PGRacing/PDM/SIM/CALCULATIONS/trace_width_proprties/external_12mm_1oz_10A_result.JPG

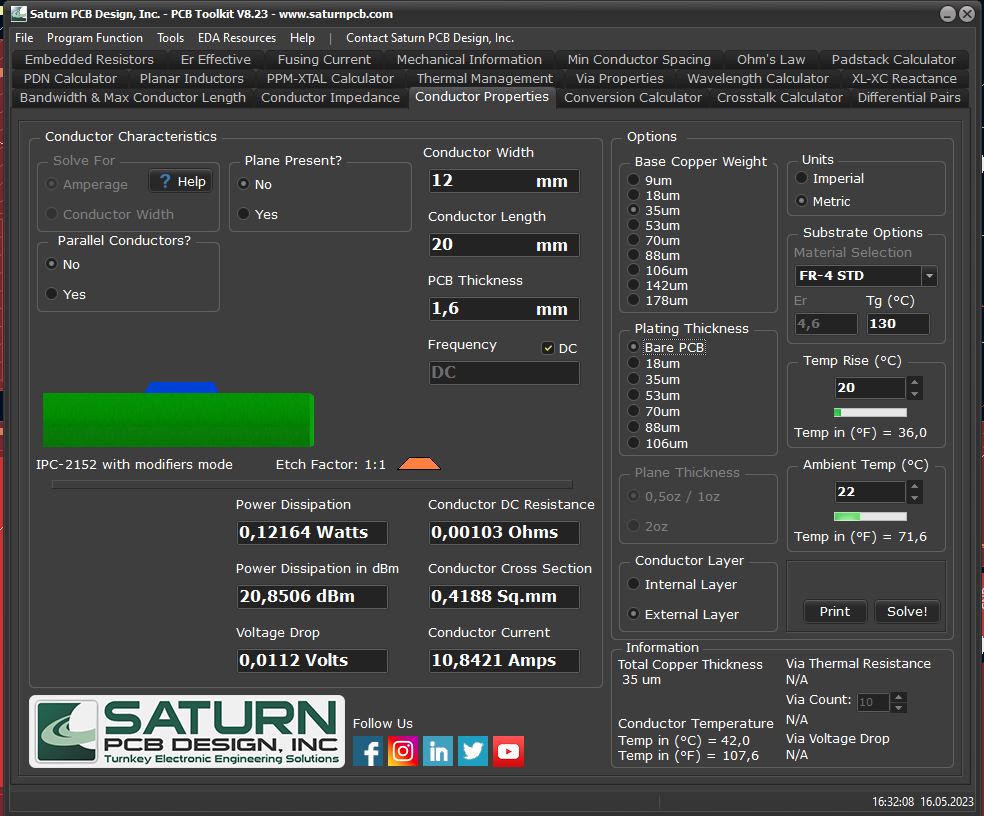
SIM/CALCULATIONS/trace_width_proprties/external_12mm_1oz_10A_result.JPG
