PGRacing/PDM/MODEL/CASE_2025/pdms_assy_2025.SLDASM

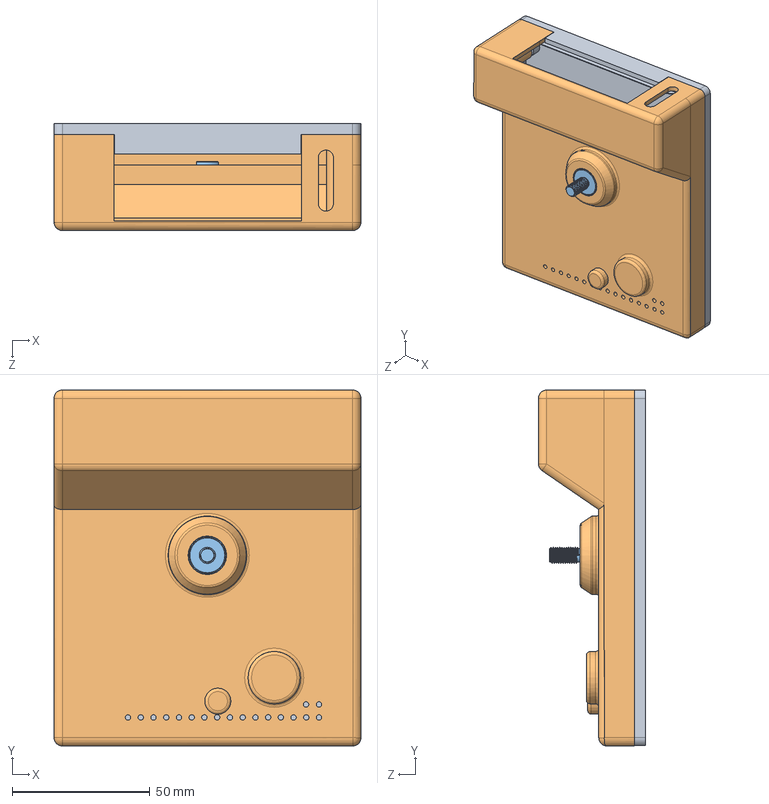
[picture p14: CAD file, 2026-06-07]
MODEL/CASE_2025/pdms_assy_2025.SLDASM
111.5 x 129.3 x 38.9 mm
pdms_thread_extender
pdms_upper_case
pdms_lower_case
