PGRacing/PDM/PCB/PDMS/pdms_additional/SPBTLE-RF/SPBTLE-RF.step

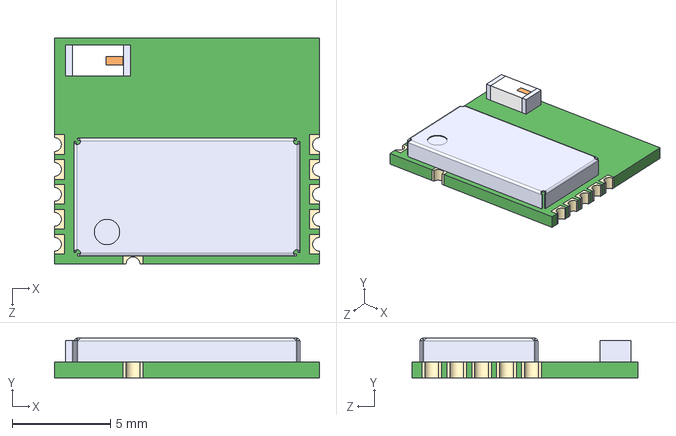
[picture p29: CAD file, 2023-05-31]
PCB/PDMS/pdms_additional/SPBTLE-RF/SPBTLE-RF.step
13.5 x 2.02 x 11.5 mm
