PGRacing/PDM/PCB/PDMS/pdms_additional/WS2812B-2020/WS2812B-2020.stp

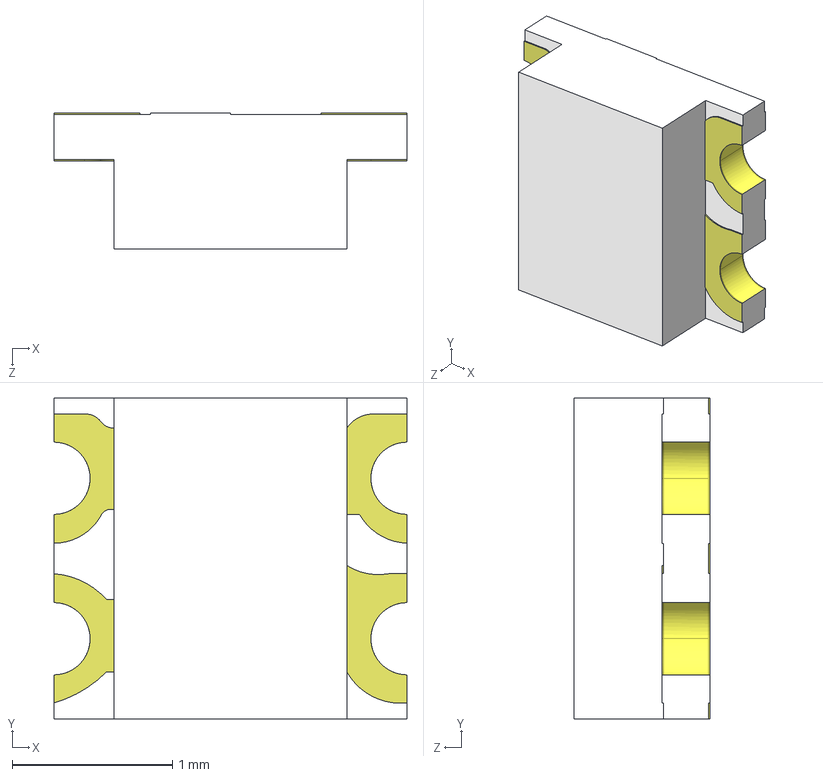
[picture p30: CAD file, 2023-05-21]
PCB/PDMS/pdms_additional/WS2812B-2020/WS2812B-2020.stp
2.20 x 2.00 x 0.85 mm
