PGRacing/PDM/MODEL/CASE_2025/pdms_thread_extender.SLDPRT

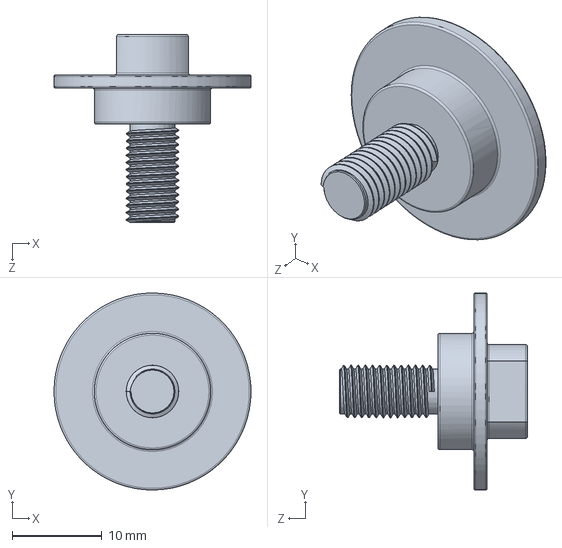
[picture p31: CAD file, 2026-06-07]
MODEL/CASE_2025/pdms_thread_extender.SLDPRT
22.0 x 22.0 x 21.0 mm
