PGRacing/PDM/MODEL/CASE_2024/upper.SLDPRT

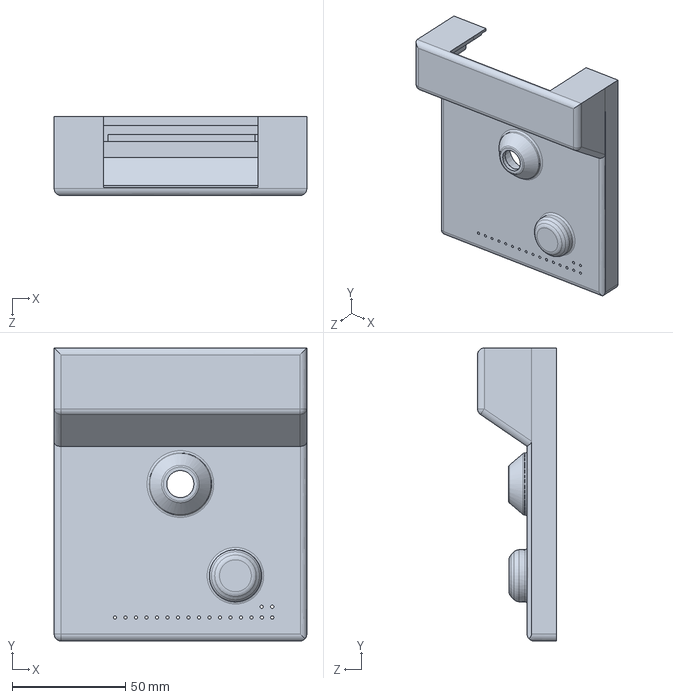
[picture p32: CAD file, 2026-06-07]
MODEL/CASE_2024/upper.SLDPRT
111.5 x 129.3 x 34.9 mm
