PGRacing/PDM/MODEL/CASE_2025/pdms_lower_case.SLDPRT

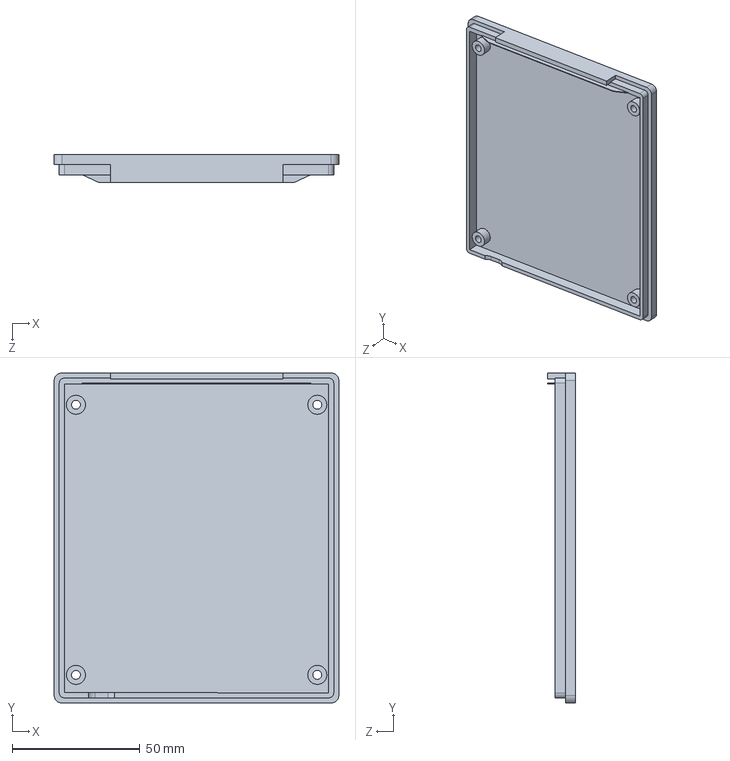
[picture p33: CAD file, 2026-06-07]
MODEL/CASE_2025/pdms_lower_case.SLDPRT
111.5 x 129.2 x 11.1 mm
