PGRacing/PDM/MODEL/CASE_2025/pdms_upper_case.SLDPRT

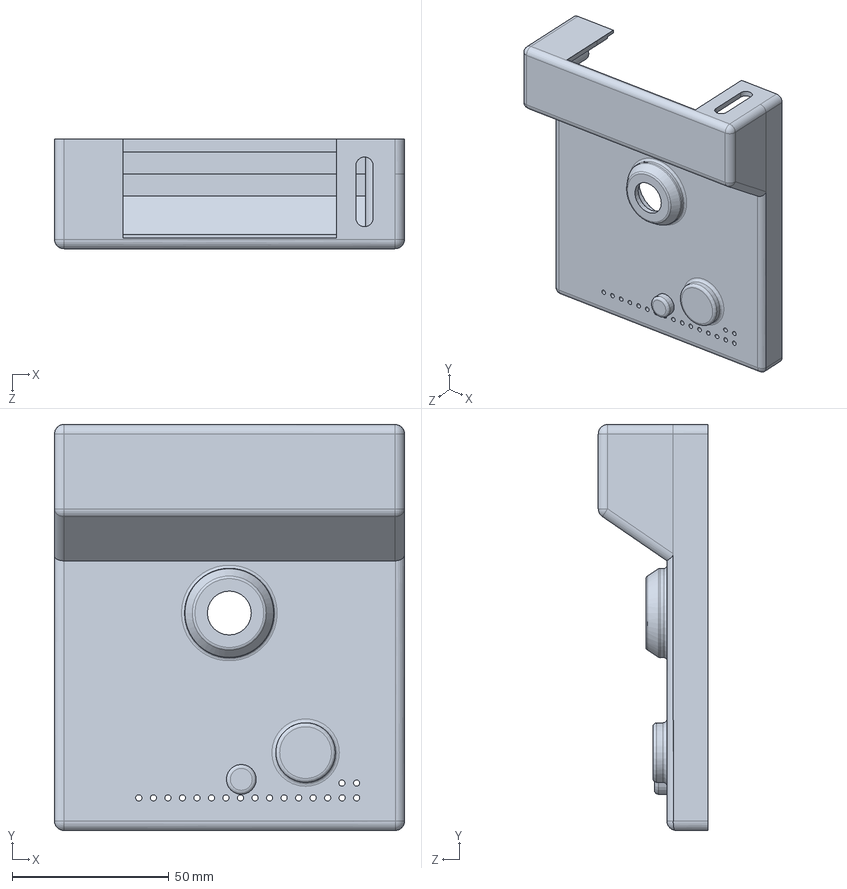
[picture p34: CAD file, 2026-06-07]
MODEL/CASE_2025/pdms_upper_case.SLDPRT
111.5 x 129.3 x 34.9 mm
