PGRacing/PDM/SIM/CALCULATIONS/trace_width_proprties/inner_12mm_0.5oz_7A_result.JPG

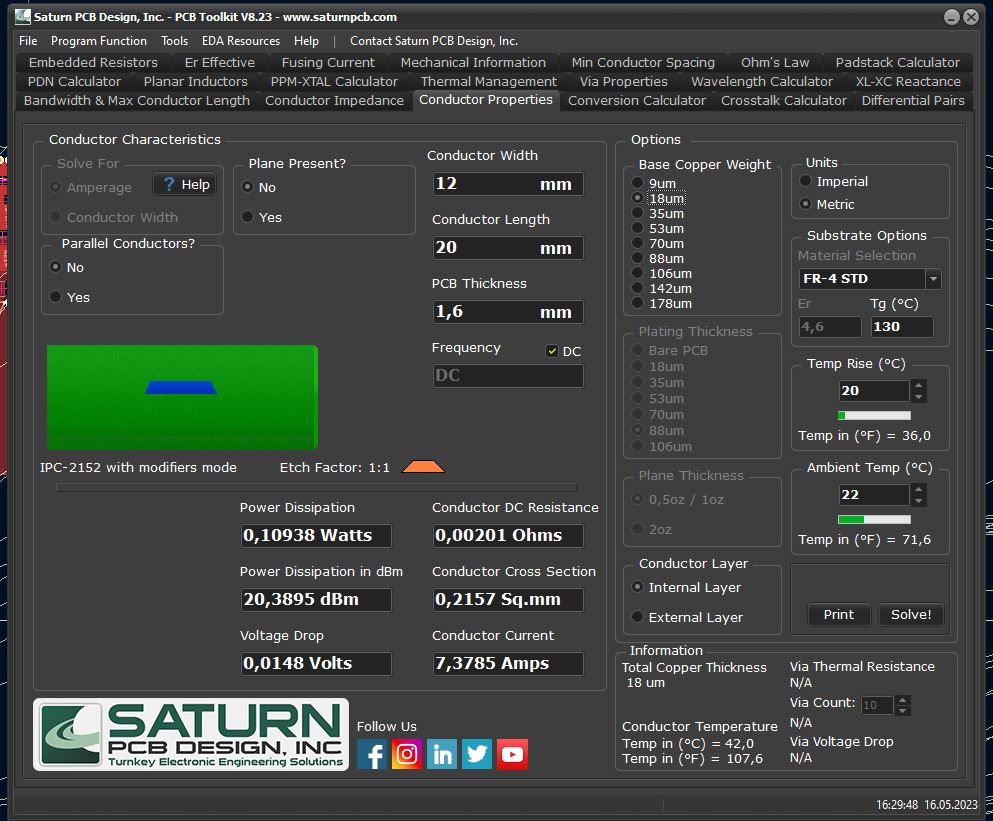
SIM/CALCULATIONS/trace_width_proprties/inner_12mm_0.5oz_7A_result.JPG
