PGRacing/PDM/CODE/PDMS/Core/Src/app/pdm.c

#include "main.h"
#include "stm32l496xx.h"
#include "stm32l4xx_it.h"
#include "stm32l4xx_hal_def.h"
#include "stm32l4xx_hal_gpio.h"
#include "FreeRTOS.h"
#include "cmsis_os2.h"
#include "task.h"
#include "tim.h"
#include "app_isotp.h"
#include "config.h"
#include "string.h"

/* HAL, MX includes */
#include "iwdg.h"
#include "pdm.h"

/////////////////////////
///////// PDM ///////////
/////////////////////////

#define UVLO_TIMER_PERIOD 50

#define PDM_RESET_GATEWAY_PATTERN_SIZE 3

extern void RTOS_SoftLimpHomeMode(void);

volatile T_PDM_CFG pdmCfg =
{
    // Platform protections
    .onInitBattCheckMaxTries = UINT32_MAX,
    .isUvloEnabled = TRUE,
    .uvloVoltageHiThreshold = 10000, // 10V
    .uvloVoltageLoThreshold = 8000,  // 8V
    .uvloTimeThreshold = 10000, // 10s
    .uvloRetainDivider = 10, 
    .minBattVolage = 6000, // In BT50010LUA TDS 5.8V minimal voltage declared

    // Others
    .useBuzzer = TRUE,
    .ledMode = 1,

    // Pointers to modules configuration
    .pOutsCfg  = &outsCfg,
    .pInsCfg  = &inputsCfg,
    .pLogicCfg = &logicCfg,
    .pTelemCfg = &telemCfg,
    .pCansCfg  = &cansCfg
};

volatile T_PDM_REG pdmReg =
{
    .status = PDM_SYS_STATUS_OK,
    .safetyState = TRUE,
    .uvloAssessment = FALSE,
    .uvloLoCounter = 0,
    .uvloHiCounter = 0,
    .uvloTimer = NULL
};

// static T_OUT_MODE PDM_OutModeInitTable[OUT_ID_MAX] = 
// {
//     OUT_MODE_STD,
//     OUT_MODE_STD,
//     OUT_MODE_STD,
//     OUT_MODE_STD,
//     OUT_MODE_STD,
//     OUT_MODE_STD,
//     OUT_MODE_STD,
//     OUT_MODE_STD,
//     OUT_MODE_STD,
//     OUT_MODE_STD,
//     OUT_MODE_STD,
//     OUT_MODE_STD,
//     OUT_MODE_STD,
//     OUT_MODE_STD,
//     OUT_MODE_STD,
//     OUT_MODE_STD,
// };

static const uint8_t resetGatewayPattern[PDM_RESET_GATEWAY_PATTERN_SIZE][8] = {{0xae, 0x3a, 0x3e, 0x2b, 0x07, 0x17, 0xc8, 0x4c}, 
                                                  {0x2d, 0x72, 0x88, 0x04, 0x9f, 0xea, 0xda, 0xc7}, 
                                                  {0x44, 0x8e, 0x0e, 0xd9, 0x56, 0xa1, 0x35, 0x0f}};

T_PDM_SYS_STATUS PDM_GetSysStatus(void)
{
    return pdmReg.status;
}

static void PDM_OutConfig(void)
{
    for(T_OUT_ID i = 0; i < OUT_ID_MAX; i++)
    {
        OUT_Reconfigure(i);
    }
}

static void PDM_SoftLimpHomeModeTimerCallback()
{
    VMUX_ReadBattVoltage();
    HAL_GPIO_WritePin(STATUS_LED_GPIO_Port, STATUS_LED_Pin, GPIO_PIN_SET);
    BUZZER_TurnOn();
    osDelay(2000);
    BUZZER_TurnOff();
    HAL_GPIO_WritePin(STATUS_LED_GPIO_Port, STATUS_LED_Pin, GPIO_PIN_RESET);
}

// Soft limp home mode with active telemetry (can bus)
static void PDM_SoftLimpHomeMode(T_PDM_SYS_STATUS status)
{
    pdmReg.status = status;
    for(T_OUT_ID id = 0; id < OUT_ID_MAX; id++)
    {
        OUT_SetState(id, OUT_STATE_ERR_LATCH);
    }

    // Check battery voltage manually each 30 seconds
    pdmReg.uvloTimer = osTimerNew((osTimerFunc_t)PDM_SoftLimpHomeModeTimerCallback, osTimerPeriodic, NULL, NULL);
    if(pdmReg.uvloTimer)
    {
        osTimerStart(pdmReg.uvloTimer, pdMS_TO_TICKS(30000));
    }
    else
    {
        LOG_ERR("PDM:: Unable to create UVLO timer!");
    }
    
    // Disable all leds
    WS2812B_DisableAll();

    // Disable all tasks except can handlers
    RTOS_SoftLimpHomeMode();
}

// Platform start
void PDM_Init(void)
{    
    vPortEnterCritical();
    
    /* ===== CONFIG LOAD ===== */
    // TODO Load settings from flash to respective flash structs(rn mockup)
    // TODO Add status return function for all initializers;
    // LOG_INFO("PDM:: Board initialized successfully");
    // LOG_INFO("PDM::Flash test");
    // int32_t flashTestRes = BSP_FLASH_TestProc();
    // LOG_VAR(flashTestRes);
    
    CONFIG_LoadConfig(CONFIG_SELECTION_A);
    /* ===== PERIPHERAL INIT ===== */

    // Initialize ADC acquisition handler
    ADCH_Init();

    // Initialize CAN communication handling 
    CANH_Init();

    // Initialize voltage measurement multiplexer
    VMUX_Init();

    // Initialize ARGB'S
    WS2812B_Init();

    /* ===== MODULES INITALIZATION ===== */
    // Initialize output module (set correct mode and state)
    PDM_OutConfig();

    // Iniitialize SPOC2 External outputs (all outputs disabled)
    SPOC2_Init();

    // Intitialize ISO-TP module
    APP_ISOTP_Init();

    // Enable debug DWT clock
    DEBUG_ARM_DWT_INIT;

    /* ===== ON INIT CHECK ===== */
    
    // Wait some time for on-board capacitors to load
    uint32_t backoffDelay = 10000000; 
    while(backoffDelay--)
    {
        __NOP();
    }

    // Verify that voltage is sufficent for normal operation (repetetive turn-on protection)
    // VMUX_ReadBattVoltage();
    // uint32_t lastBattVoltage = 0;
    
    // for(uint32_t i = 0; i < pdmCfg.onInitBattCheckMaxTries; i++)
    // {
    //     VMUX_ReadBattVoltage();
    //     lastBattVoltage = VMUX_GetBattValue();
    //     if(lastBattVoltage <= pdmCfg.minBattVolage)
    //     {
    //         backoffDelay = 10000000; 
    //         while(backoffDelay--)
    //         {
    //             __NOP();
    //         }

    //         LOG_WARN("PDM:: Insufficent battery voltage to start");
    //         LOG_VAR(lastBattVoltage);

    //         if(i == pdmCfg.onInitBattCheckMaxTries - 1)
    //         {
    //             LOG_ERR("PDM:: Unable to start battery voltage too low!");
    //             Error_Handler();
    //         }
    //     }
    //     else
    //     {
    //         // If battery voltage is sufficent to start exit loop
    //         break;
    //     }
    // }

    // Enable watchdog
    MX_IWDG_Init();
    vPortExitCritical();
}

// Get safety-line state
static void PDM_CheckSafety(void)
{
    if(HAL_GPIO_ReadPin(SAFETY_IN_GPIO_Port, SAFETY_IN_Pin) == GPIO_PIN_RESET)
    {

        pdmReg.safetyState = FALSE;
    }
    else
    {
        pdmReg.safetyState = TRUE;
    }
}

static void PDM_UVLOCallback()
{
    if(VMUX_GetBattValue() > pdmCfg.uvloVoltageHiThreshold)
    {
        pdmReg.uvloHiCounter++;
        if(pdmReg.uvloHiCounter > (pdmCfg.uvloTimeThreshold / (UVLO_TIMER_PERIOD * pdmCfg.uvloRetainDivider)))
        {
            osTimerStop(pdmReg.uvloTimer);
            pdmReg.uvloTimer = NULL;
            pdmReg.uvloAssessment = FALSE;
            pdmReg.uvloHiCounter = 0;
            pdmReg.uvloLoCounter = 0;
            LOG_INFO("PDM:: UVLO Battery voltage retained, returing to normal operation");
            osTimerDelete(pdmReg.uvloTimer);
            return;
        }
    }
    else
    {
        pdmReg.uvloLoCounter++;
        if(pdmReg.uvloLoCounter > (pdmCfg.uvloTimeThreshold / UVLO_TIMER_PERIOD))
        {
            osTimerStop(pdmReg.uvloTimer);
            pdmReg.uvloTimer = NULL;
            pdmReg.uvloAssessment = FALSE;
            pdmReg.uvloHiCounter = 0;
            pdmReg.uvloLoCounter = 0;
            LOG_ERR("PDM:: UVLO detected turning off!");
            PDM_SoftLimpHomeMode(PDM_SYS_STATUS_UVLO);
            return;
        }
    }

}

// Check under voltage protection
static void PDM_CheckUVLO(void)
{
    // Trigger checking on timer
    if(VMUX_GetBattValue() < pdmCfg.uvloVoltageLoThreshold)
    {
        LOG_WARN("PDM:: First UVLO trigger detected");
        pdmReg.uvloAssessment = TRUE;
        // Create timer for retry execution routine
        pdmReg.uvloTimer = osTimerNew((osTimerFunc_t)PDM_UVLOCallback, osTimerPeriodic, NULL, NULL);
        if(pdmReg.uvloTimer)
        {
            osTimerStart(pdmReg.uvloTimer, pdMS_TO_TICKS(UVLO_TIMER_PERIOD));
        }
        else
        {
            LOG_ERR("PDM:: Unable to create UVLO timer!");
        }
    }
}

bool PDM_GetSafetyState(void)
{
    return pdmReg.safetyState;
}

/// @brief Allow to reset device via CAN when specific pattern is sent to CAN.
/// @param id Frame ID
/// @param data Frame data
/// @param size Frame data size
void PDM_CANResetGateway(uint32_t id, uint8_t* data, uint32_t size)
{
    if(size != 8)
    {
        pdmReg.resetGwCounter = 0;
        return;
    }
    else if(size == 8 && 0 == memcmp(data, resetGatewayPattern[pdmReg.resetGwCounter], 8))
    {
        pdmReg.resetGwCounter++;
        if(pdmReg.resetGwCounter >= PDM_RESET_GATEWAY_PATTERN_SIZE)
        {
            pdmReg.resetGwCounter = 0;
            LOG_INFO("PDM:: Reset gateway pattern detected, reseting device");
            NVIC_SystemReset();
        }
    }
    else
    {
        pdmReg.resetGwCounter = 0;
    }
}


void pdmTaskStart(void *argument)
{       
    /* ---> Platform initialized (PDM_Init) in main.c before scheduler start */
    LOG_INFO("PDM:: Task start");
    for(;;)
    {
        T_LOGIC_REG* logicReg = LOGIC_Evaluate();
        for(T_OUT_ID i = 0; i < OUT_ID_MAX; i++)
        {
            if(FALSE == OUT_IsSafetyLineDependent(i))
            {
                OUT_SetState(i, logicReg[i].state);
            }
            else
            {
                OUT_SetState(i, logicReg[i].state && pdmReg.safetyState);
            }
        }
        PDM_CheckSafety();

        // Check undervoltage if no ongoing assesment
        if(pdmCfg.isUvloEnabled == TRUE &&
            pdmReg.uvloAssessment == FALSE &&
            pdmReg.status == PDM_SYS_STATUS_OK)
        {
            PDM_CheckUVLO();
        }
      
        osDelay(pdMS_TO_TICKS(1));
    }
}
