PGRacing/PDM/CODE/PDMS/Core/Src/adc.c

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
/* Includes ------------------------------------------------------------------*/
#include "adc.h"

/* USER CODE BEGIN 0 */
#include "FreeRTOS.h"
#include "task.h"
#include "cmsis_os2.h"
#include "main.h"
#include "tim.h"
#include "semphr.h"
#include "stm32l4xx_hal_adc.h"
#include "pdm.h"
#include <string.h>

// Required for ADC PWM cowork
#include "bsp_out.h"

extern SemaphoreHandle_t adc1ConvReadySemaphore;
extern SemaphoreHandle_t adc2ConvReadySemaphore;

#define ADC_12BIT_MAX_VALUE 4096

#define ADC2_SAMPLING_RATE 200 // Hz, frequency of ADC2 conversion

/* USER CODE END 0 */

ADC_HandleTypeDef hadc1;
ADC_HandleTypeDef hadc2;
ADC_HandleTypeDef hadc3;
DMA_HandleTypeDef hdma_adc1;
DMA_HandleTypeDef hdma_adc2;

/* ADC1 init function */
void MX_ADC1_Init(void)
{

  ADC_MultiModeTypeDef multimode = {0};
  ADC_ChannelConfTypeDef sConfig = {0};

  /** Common config
  */
  hadc1.Instance = ADC1;
  hadc1.Init.ClockPrescaler = ADC_CLOCK_ASYNC_DIV1;
  hadc1.Init.Resolution = ADC_RESOLUTION_12B;
  hadc1.Init.DataAlign = ADC_DATAALIGN_RIGHT;
  hadc1.Init.ScanConvMode = ADC_SCAN_ENABLE;
  hadc1.Init.EOCSelection = ADC_EOC_SEQ_CONV;
  hadc1.Init.LowPowerAutoWait = DISABLE;
  hadc1.Init.ContinuousConvMode = DISABLE;
  hadc1.Init.NbrOfConversion = 8;
  hadc1.Init.DiscontinuousConvMode = DISABLE;
  hadc1.Init.ExternalTrigConv = ADC_EXTERNALTRIG_T15_TRGO;
  hadc1.Init.ExternalTrigConvEdge = ADC_EXTERNALTRIGCONVEDGE_RISING;
  hadc1.Init.DMAContinuousRequests = ENABLE;
  hadc1.Init.Overrun = ADC_OVR_DATA_OVERWRITTEN;
  hadc1.Init.OversamplingMode = ENABLE;
  hadc1.Init.Oversampling.Ratio = ADC_OVERSAMPLING_RATIO_16;
  hadc1.Init.Oversampling.RightBitShift = ADC_RIGHTBITSHIFT_4;
  hadc1.Init.Oversampling.TriggeredMode = ADC_TRIGGEREDMODE_SINGLE_TRIGGER;
  hadc1.Init.Oversampling.OversamplingStopReset = ADC_REGOVERSAMPLING_CONTINUED_MODE;
  if (HAL_ADC_Init(&hadc1) != HAL_OK)
  {
    Error_Handler();
  }

  /** Configure the ADC multi-mode
  */
  multimode.Mode = ADC_MODE_INDEPENDENT;
  if (HAL_ADCEx_MultiModeConfigChannel(&hadc1, &multimode) != HAL_OK)
  {
    Error_Handler();
  }

  /** Configure Regular Channel
  */
  sConfig.Channel = ADC_CHANNEL_8;
  sConfig.Rank = ADC_REGULAR_RANK_1;
  sConfig.SamplingTime = ADC_SAMPLETIME_12CYCLES_5;
  sConfig.SingleDiff = ADC_SINGLE_ENDED;
  sConfig.OffsetNumber = ADC_OFFSET_NONE;
  sConfig.Offset = 0;
  if (HAL_ADC_ConfigChannel(&hadc1, &sConfig) != HAL_OK)
  {
    Error_Handler();
  }

  /** Configure Regular Channel
  */
  sConfig.Channel = ADC_CHANNEL_7;
  sConfig.Rank = ADC_REGULAR_RANK_2;
  if (HAL_ADC_ConfigChannel(&hadc1, &sConfig) != HAL_OK)
  {
    Error_Handler();
  }

  /** Configure Regular Channel
  */
  sConfig.Channel = ADC_CHANNEL_6;
  sConfig.Rank = ADC_REGULAR_RANK_3;
  if (HAL_ADC_ConfigChannel(&hadc1, &sConfig) != HAL_OK)
  {
    Error_Handler();
  }

  /** Configure Regular Channel
  */
  sConfig.Channel = ADC_CHANNEL_5;
  sConfig.Rank = ADC_REGULAR_RANK_4;
  if (HAL_ADC_ConfigChannel(&hadc1, &sConfig) != HAL_OK)
  {
    Error_Handler();
  }

  /** Configure Regular Channel
  */
  sConfig.Channel = ADC_CHANNEL_4;
  sConfig.Rank = ADC_REGULAR_RANK_5;
  if (HAL_ADC_ConfigChannel(&hadc1, &sConfig) != HAL_OK)
  {
    Error_Handler();
  }

  /** Configure Regular Channel
  */
  sConfig.Channel = ADC_CHANNEL_3;
  sConfig.Rank = ADC_REGULAR_RANK_6;
  if (HAL_ADC_ConfigChannel(&hadc1, &sConfig) != HAL_OK)
  {
    Error_Handler();
  }

  /** Configure Regular Channel
  */
  sConfig.Channel = ADC_CHANNEL_2;
  sConfig.Rank = ADC_REGULAR_RANK_7;
  if (HAL_ADC_ConfigChannel(&hadc1, &sConfig) != HAL_OK)
  {
    Error_Handler();
  }

  /** Configure Regular Channel
  */
  sConfig.Channel = ADC_CHANNEL_1;
  sConfig.Rank = ADC_REGULAR_RANK_8;
  if (HAL_ADC_ConfigChannel(&hadc1, &sConfig) != HAL_OK)
  {
    Error_Handler();
  }
}
/* ADC2 init function */
void MX_ADC2_Init(void)
{

  ADC_ChannelConfTypeDef sConfig = {0};

  /** Common config
  */
  hadc2.Instance = ADC2;
  hadc2.Init.ClockPrescaler = ADC_CLOCK_ASYNC_DIV1;
  hadc2.Init.Resolution = ADC_RESOLUTION_12B;
  hadc2.Init.DataAlign = ADC_DATAALIGN_RIGHT;
  hadc2.Init.ScanConvMode = ADC_SCAN_ENABLE;
  hadc2.Init.EOCSelection = ADC_EOC_SEQ_CONV;
  hadc2.Init.LowPowerAutoWait = DISABLE;
  hadc2.Init.ContinuousConvMode = DISABLE;
  hadc2.Init.NbrOfConversion = 8;
  hadc2.Init.DiscontinuousConvMode = DISABLE;
  hadc2.Init.ExternalTrigConv = ADC_EXTERNALTRIG_T8_TRGO;
  hadc2.Init.ExternalTrigConvEdge = ADC_EXTERNALTRIGCONVEDGE_RISING;
  hadc2.Init.DMAContinuousRequests = ENABLE;
  hadc2.Init.Overrun = ADC_OVR_DATA_PRESERVED;
  hadc2.Init.OversamplingMode = DISABLE;
  if (HAL_ADC_Init(&hadc2) != HAL_OK)
  {
    Error_Handler();
  }

  /** Configure Regular Channel
  */
  sConfig.Channel = ADC_CHANNEL_16;
  sConfig.Rank = ADC_REGULAR_RANK_1;
  sConfig.SamplingTime = ADC_SAMPLETIME_12CYCLES_5;
  sConfig.SingleDiff = ADC_SINGLE_ENDED;
  sConfig.OffsetNumber = ADC_OFFSET_NONE;
  sConfig.Offset = 0;
  if (HAL_ADC_ConfigChannel(&hadc2, &sConfig) != HAL_OK)
  {
    Error_Handler();
  }

  /** Configure Regular Channel
  */
  sConfig.Channel = ADC_CHANNEL_15;
  sConfig.Rank = ADC_REGULAR_RANK_2;
  if (HAL_ADC_ConfigChannel(&hadc2, &sConfig) != HAL_OK)
  {
    Error_Handler();
  }

  /** Configure Regular Channel
  */
  sConfig.Channel = ADC_CHANNEL_14;
  sConfig.Rank = ADC_REGULAR_RANK_3;
  if (HAL_ADC_ConfigChannel(&hadc2, &sConfig) != HAL_OK)
  {
    Error_Handler();
  }

  /** Configure Regular Channel
  */
  sConfig.Channel = ADC_CHANNEL_13;
  sConfig.Rank = ADC_REGULAR_RANK_4;
  if (HAL_ADC_ConfigChannel(&hadc2, &sConfig) != HAL_OK)
  {
    Error_Handler();
  }

  /** Configure Regular Channel
  */
  sConfig.Channel = ADC_CHANNEL_12;
  sConfig.Rank = ADC_REGULAR_RANK_5;
  if (HAL_ADC_ConfigChannel(&hadc2, &sConfig) != HAL_OK)
  {
    Error_Handler();
  }

  /** Configure Regular Channel
  */
  sConfig.Channel = ADC_CHANNEL_11;
  sConfig.Rank = ADC_REGULAR_RANK_6;
  if (HAL_ADC_ConfigChannel(&hadc2, &sConfig) != HAL_OK)
  {
    Error_Handler();
  }

  /** Configure Regular Channel
  */
  sConfig.Channel = ADC_CHANNEL_10;
  sConfig.Rank = ADC_REGULAR_RANK_7;
  if (HAL_ADC_ConfigChannel(&hadc2, &sConfig) != HAL_OK)
  {
    Error_Handler();
  }

  /** Configure Regular Channel
  */
  sConfig.Channel = ADC_CHANNEL_9;
  sConfig.Rank = ADC_REGULAR_RANK_8;
  if (HAL_ADC_ConfigChannel(&hadc2, &sConfig) != HAL_OK)
  {
    Error_Handler();
  }
}
/* ADC3 init function */
void MX_ADC3_Init(void)
{

  ADC_ChannelConfTypeDef sConfig = {0};

  /** Common config
  */
  hadc3.Instance = ADC3;
  hadc3.Init.ClockPrescaler = ADC_CLOCK_ASYNC_DIV1;
  hadc3.Init.Resolution = ADC_RESOLUTION_12B;
  hadc3.Init.DataAlign = ADC_DATAALIGN_RIGHT;
  hadc3.Init.ScanConvMode = ADC_SCAN_DISABLE;
  hadc3.Init.EOCSelection = ADC_EOC_SEQ_CONV;
  hadc3.Init.LowPowerAutoWait = DISABLE;
  hadc3.Init.ContinuousConvMode = ENABLE;
  hadc3.Init.NbrOfConversion = 1;
  hadc3.Init.DiscontinuousConvMode = DISABLE;
  hadc3.Init.ExternalTrigConv = ADC_SOFTWARE_START;
  hadc3.Init.ExternalTrigConvEdge = ADC_EXTERNALTRIGCONVEDGE_NONE;
  hadc3.Init.DMAContinuousRequests = DISABLE;
  hadc3.Init.Overrun = ADC_OVR_DATA_OVERWRITTEN;
  hadc3.Init.OversamplingMode = DISABLE;
  if (HAL_ADC_Init(&hadc3) != HAL_OK)
  {
    Error_Handler();
  }

  /** Configure Regular Channel
  */
  sConfig.Channel = ADC_CHANNEL_6;
  sConfig.Rank = ADC_REGULAR_RANK_1;
  sConfig.SamplingTime = ADC_SAMPLETIME_2CYCLES_5;
  sConfig.SingleDiff = ADC_SINGLE_ENDED;
  sConfig.OffsetNumber = ADC_OFFSET_NONE;
  sConfig.Offset = 0;
  if (HAL_ADC_ConfigChannel(&hadc3, &sConfig) != HAL_OK)
  {
    Error_Handler();
  }
}

static uint32_t HAL_RCC_ADC_CLK_ENABLED=0;

void HAL_ADC_MspInit(ADC_HandleTypeDef* adcHandle)
{

  GPIO_InitTypeDef GPIO_InitStruct = {0};
  if(adcHandle->Instance==ADC1)
  {
    /* ADC1 clock enable */
    HAL_RCC_ADC_CLK_ENABLED++;
    if(HAL_RCC_ADC_CLK_ENABLED==1){
      __HAL_RCC_ADC_CLK_ENABLE();
    }

    __HAL_RCC_GPIOC_CLK_ENABLE();
    __HAL_RCC_GPIOA_CLK_ENABLE();
    /**ADC1 GPIO Configuration
    PC0     ------> ADC1_IN1
    PC1     ------> ADC1_IN2
    PC2     ------> ADC1_IN3
    PC3     ------> ADC1_IN4
    PA0     ------> ADC1_IN5
    PA1     ------> ADC1_IN6
    PA2     ------> ADC1_IN7
    PA3     ------> ADC1_IN8
    */
    GPIO_InitStruct.Pin = GPIO_PIN_0|GPIO_PIN_1|GPIO_PIN_2|GPIO_PIN_3;
    GPIO_InitStruct.Mode = GPIO_MODE_ANALOG;
    GPIO_InitStruct.Pull = GPIO_NOPULL;
    HAL_GPIO_Init(GPIOC, &GPIO_InitStruct);

    GPIO_InitStruct.Pin = GPIO_PIN_0|GPIO_PIN_1|GPIO_PIN_2|GPIO_PIN_3;
    GPIO_InitStruct.Mode = GPIO_MODE_ANALOG;
    GPIO_InitStruct.Pull = GPIO_NOPULL;
    HAL_GPIO_Init(GPIOA, &GPIO_InitStruct);

    /* ADC1 DMA Init */
    /* ADC1 Init */
    hdma_adc1.Instance = DMA1_Channel1;
    hdma_adc1.Init.Request = DMA_REQUEST_0;
    hdma_adc1.Init.Direction = DMA_PERIPH_TO_MEMORY;
    hdma_adc1.Init.PeriphInc = DMA_PINC_DISABLE;
    hdma_adc1.Init.MemInc = DMA_MINC_ENABLE;
    hdma_adc1.Init.PeriphDataAlignment = DMA_PDATAALIGN_HALFWORD;
    hdma_adc1.Init.MemDataAlignment = DMA_MDATAALIGN_HALFWORD;
    hdma_adc1.Init.Mode = DMA_CIRCULAR;
    hdma_adc1.Init.Priority = DMA_PRIORITY_HIGH;
    if (HAL_DMA_Init(&hdma_adc1) != HAL_OK)
    {
      Error_Handler();
    }

    __HAL_LINKDMA(adcHandle,DMA_Handle,hdma_adc1);

    /* ADC1 interrupt Init */
    HAL_NVIC_SetPriority(ADC1_2_IRQn, 5, 0);
    HAL_NVIC_EnableIRQ(ADC1_2_IRQn);
  }
  else if(adcHandle->Instance==ADC2)
  {
    /* ADC2 clock enable */
    HAL_RCC_ADC_CLK_ENABLED++;
    if(HAL_RCC_ADC_CLK_ENABLED==1){
      __HAL_RCC_ADC_CLK_ENABLE();
    }

    __HAL_RCC_GPIOA_CLK_ENABLE();
    __HAL_RCC_GPIOC_CLK_ENABLE();
    __HAL_RCC_GPIOB_CLK_ENABLE();
    /**ADC2 GPIO Configuration
    PA4     ------> ADC2_IN9
    PA5     ------> ADC2_IN10
    PA6     ------> ADC2_IN11
    PA7     ------> ADC2_IN12
    PC4     ------> ADC2_IN13
    PC5     ------> ADC2_IN14
    PB0     ------> ADC2_IN15
    PB1     ------> ADC2_IN16
    */
    GPIO_InitStruct.Pin = GPIO_PIN_4|GPIO_PIN_5|GPIO_PIN_6|GPIO_PIN_7;
    GPIO_InitStruct.Mode = GPIO_MODE_ANALOG;
    GPIO_InitStruct.Pull = GPIO_NOPULL;
    HAL_GPIO_Init(GPIOA, &GPIO_InitStruct);

    GPIO_InitStruct.Pin = GPIO_PIN_4|GPIO_PIN_5;
    GPIO_InitStruct.Mode = GPIO_MODE_ANALOG;
    GPIO_InitStruct.Pull = GPIO_NOPULL;
    HAL_GPIO_Init(GPIOC, &GPIO_InitStruct);

    GPIO_InitStruct.Pin = GPIO_PIN_0|GPIO_PIN_1;
    GPIO_InitStruct.Mode = GPIO_MODE_ANALOG;
    GPIO_InitStruct.Pull = GPIO_NOPULL;
    HAL_GPIO_Init(GPIOB, &GPIO_InitStruct);

    /* ADC2 DMA Init */
    /* ADC2 Init */
    hdma_adc2.Instance = DMA1_Channel2;
    hdma_adc2.Init.Request = DMA_REQUEST_0;
    hdma_adc2.Init.Direction = DMA_PERIPH_TO_MEMORY;
    hdma_adc2.Init.PeriphInc = DMA_PINC_DISABLE;
    hdma_adc2.Init.MemInc = DMA_MINC_ENABLE;
    hdma_adc2.Init.PeriphDataAlignment = DMA_PDATAALIGN_HALFWORD;
    hdma_adc2.Init.MemDataAlignment = DMA_MDATAALIGN_HALFWORD;
    hdma_adc2.Init.Mode = DMA_CIRCULAR;
    hdma_adc2.Init.Priority = DMA_PRIORITY_HIGH;
    if (HAL_DMA_Init(&hdma_adc2) != HAL_OK)
    {
      Error_Handler();
    }

    __HAL_LINKDMA(adcHandle,DMA_Handle,hdma_adc2);

    /* ADC2 interrupt Init */
    HAL_NVIC_SetPriority(ADC1_2_IRQn, 5, 0);
    HAL_NVIC_EnableIRQ(ADC1_2_IRQn);
  }
  else if(adcHandle->Instance==ADC3)
  {
    /* ADC3 clock enable */
    HAL_RCC_ADC_CLK_ENABLED++;
    if(HAL_RCC_ADC_CLK_ENABLED==1){
      __HAL_RCC_ADC_CLK_ENABLE();
    }

    __HAL_RCC_GPIOF_CLK_ENABLE();
    /**ADC3 GPIO Configuration
    PF3     ------> ADC3_IN6
    PF4     ------> ADC3_IN7
    PF5     ------> ADC3_IN8
    PF10     ------> ADC3_IN13
    */
    GPIO_InitStruct.Pin = GPIO_PIN_3|GPIO_PIN_4|GPIO_PIN_5|GPIO_PIN_10;
    GPIO_InitStruct.Mode = GPIO_MODE_ANALOG;
    GPIO_InitStruct.Pull = GPIO_NOPULL;
    HAL_GPIO_Init(GPIOF, &GPIO_InitStruct);

  }
}

void HAL_ADC_MspDeInit(ADC_HandleTypeDef* adcHandle)
{

  if(adcHandle->Instance==ADC1)
  {
    /* Peripheral clock disable */
    HAL_RCC_ADC_CLK_ENABLED--;
    if(HAL_RCC_ADC_CLK_ENABLED==0){
      __HAL_RCC_ADC_CLK_DISABLE();
    }

    /**ADC1 GPIO Configuration
    PC0     ------> ADC1_IN1
    PC1     ------> ADC1_IN2
    PC2     ------> ADC1_IN3
    PC3     ------> ADC1_IN4
    PA0     ------> ADC1_IN5
    PA1     ------> ADC1_IN6
    PA2     ------> ADC1_IN7
    PA3     ------> ADC1_IN8
    */
    HAL_GPIO_DeInit(GPIOC, GPIO_PIN_0|GPIO_PIN_1|GPIO_PIN_2|GPIO_PIN_3);

    HAL_GPIO_DeInit(GPIOA, GPIO_PIN_0|GPIO_PIN_1|GPIO_PIN_2|GPIO_PIN_3);

    /* ADC1 DMA DeInit */
    HAL_DMA_DeInit(adcHandle->DMA_Handle);

    /* ADC1 interrupt Deinit */
  /* USER CODE BEGIN ADC1:ADC1_2_IRQn disable */
    /**
    * Uncomment the line below to disable the "ADC1_2_IRQn" interrupt
    * Be aware, disabling shared interrupt may affect other IPs
    */
    /* HAL_NVIC_DisableIRQ(ADC1_2_IRQn); */
  /* USER CODE END ADC1:ADC1_2_IRQn disable */

  }
  else if(adcHandle->Instance==ADC2)
  {
    /* Peripheral clock disable */
    HAL_RCC_ADC_CLK_ENABLED--;
    if(HAL_RCC_ADC_CLK_ENABLED==0){
      __HAL_RCC_ADC_CLK_DISABLE();
    }

    /**ADC2 GPIO Configuration
    PA4     ------> ADC2_IN9
    PA5     ------> ADC2_IN10
    PA6     ------> ADC2_IN11
    PA7     ------> ADC2_IN12
    PC4     ------> ADC2_IN13
    PC5     ------> ADC2_IN14
    PB0     ------> ADC2_IN15
    PB1     ------> ADC2_IN16
    */
    HAL_GPIO_DeInit(GPIOA, GPIO_PIN_4|GPIO_PIN_5|GPIO_PIN_6|GPIO_PIN_7);

    HAL_GPIO_DeInit(GPIOC, GPIO_PIN_4|GPIO_PIN_5);

    HAL_GPIO_DeInit(GPIOB, GPIO_PIN_0|GPIO_PIN_1);

    /* ADC2 DMA DeInit */
    HAL_DMA_DeInit(adcHandle->DMA_Handle);

    /* ADC2 interrupt Deinit */
  /* USER CODE BEGIN ADC2:ADC1_2_IRQn disable */
    /**
    * Uncomment the line below to disable the "ADC1_2_IRQn" interrupt
    * Be aware, disabling shared interrupt may affect other IPs
    */
    /* HAL_NVIC_DisableIRQ(ADC1_2_IRQn); */
  /* USER CODE END ADC2:ADC1_2_IRQn disable */

  }
  else if(adcHandle->Instance==ADC3)
  {
    /* Peripheral clock disable */
    HAL_RCC_ADC_CLK_ENABLED--;
    if(HAL_RCC_ADC_CLK_ENABLED==0){
      __HAL_RCC_ADC_CLK_DISABLE();
    }

    /**ADC3 GPIO Configuration
    PF3     ------> ADC3_IN6
    PF4     ------> ADC3_IN7
    PF5     ------> ADC3_IN8
    PF10     ------> ADC3_IN13
    */
    HAL_GPIO_DeInit(GPIOF, GPIO_PIN_3|GPIO_PIN_4|GPIO_PIN_5|GPIO_PIN_10);

  }
}

/* USER CODE BEGIN 1 */
uint16_t adc1RawData[ADC1_CHANNEL_COUNT];
uint16_t adc2RawData[ADC2_CHANNEL_COUNT];

uint16_t adc1LastValidRawData[ADC1_CHANNEL_COUNT] = {0};

/* Current readout averaging */
volatile uint16_t adc1MedianCounter = 0;

volatile uint16_t adc1MedianBuffer[ADC1_CHANNEL_COUNT][ADC1_SW_OVERSAMPLING_RATIO] = {0};
volatile uint16_t adc1MedianBufferShadow[ADC1_CHANNEL_COUNT][ADC1_SW_OVERSAMPLING_RATIO] = {0};

#ifdef DEBUG
volatile static uint32_t DWTfastADC1TS = 0;
volatile static uint32_t DWTfastADC1DLT = 0;

volatile static uint32_t DWTslowADC1TS = 0;
volatile static uint32_t DWTslowADC1DLT = 0;
#endif

void HAL_ADC_ConvCpltCallback(ADC_HandleTypeDef *hadc)
{
    ASSERT(adc1ConvReadySemaphore);
    ASSERT(adc2ConvReadySemaphore);
    if(hadc == &hadc1)
    {
#ifdef DEBUG
      DWTfastADC1DLT = DEBUG_ARM_CLOCKS_TO_US(DEBUG_ARM_GET_TIME - DWTfastADC1TS);
      DWTfastADC1TS = DEBUG_ARM_GET_TIME;
#endif
      for(uint8_t i = 0; i < ADC1_CHANNEL_COUNT; i++)
      {
        // WARN Currently ADC channel maps directly to BSP_OUT_ID, so we can use it to check if measurement is valid
        // If this changes in the future, need to implement separate mapping and validity checking
        if(BSP_OUT_IsPWM(i) ==  TRUE)
        {
          if(BSP_OUT_SenseValid(i) == TRUE)
          {
            adc1MedianBuffer[i][adc1MedianCounter] = adc1RawData[i];
            //adc1LastValidRawData[i] = adc1RawData[i];
          }
          else
          {
            adc1MedianBuffer[i][adc1MedianCounter] = 0; // Invalid measurement, set to last valid or 0
          }
        }
        else // Std output simple median filter buffer fill
        {
          adc1MedianBuffer[i][adc1MedianCounter] = adc1RawData[i];
        }
      }
      adc1MedianCounter++;

      // If enough samples collected for oversampling, calculate median and average
      if(adc1MedianCounter >= ADC1_SW_OVERSAMPLING_RATIO)
      {
        adc1MedianCounter = 0;
        memcpy((void*)adc1MedianBufferShadow, (void*)adc1MedianBuffer, sizeof(adc1MedianBuffer));
        // Notify task that new ADC1 data is ready
        portBASE_TYPE xHigherPriorityTaskWoken;
        xHigherPriorityTaskWoken = pdFALSE;
        if(adc1ConvReadySemaphore != NULL)
        {
#ifdef DEBUG
          DWTslowADC1DLT = DEBUG_ARM_CLOCKS_TO_US(DEBUG_ARM_GET_TIME - DWTslowADC1TS);
          DWTslowADC1TS = DEBUG_ARM_GET_TIME;
#endif
          xSemaphoreGiveFromISR(adc1ConvReadySemaphore, &xHigherPriorityTaskWoken);
        }
        portYIELD_FROM_ISR(xHigherPriorityTaskWoken);
      }

    }else if(hadc == &hadc2)
    {
      portBASE_TYPE xHigherPriorityTaskWoken;
      xHigherPriorityTaskWoken = pdFALSE;
      
      if(adc2ConvReadySemaphore != NULL)
      {
        xSemaphoreGiveFromISR(adc2ConvReadySemaphore, &xHigherPriorityTaskWoken);
      }
      portYIELD_FROM_ISR(xHigherPriorityTaskWoken);
    }
    else if(hadc == &hadc3)
    {

    }
}


void HAL_ADC_ConvHalfCpltCallback(ADC_HandleTypeDef *hadc)
{
  __NOP();
}


void ADC1_Init(void)
{ 
    /* Timer 15 configured to execute ADC1 conversion each 0.1ms / 10kHz */
    HAL_TIM_Base_Start(&htim15);

    /* Start ADC in DMA mode */
    // ADC1 - BSP current sensors
    HAL_ADC_Start_DMA(&hadc1, (uint32_t*)adc1RawData, ADC1_CHANNEL_COUNT);

    // ADC Calibration for better accuracy TODO - not tested
    // HAL_ADCEx_Calibration_Start(&hadc1, ADC_SINGLE_ENDED);
    // HAL_ADCEx_Calibration_Start(&hadc2, ADC_SINGLE_ENDED);
    // HAL_ADCEx_Calibration_Start(&hadc3, ADC_SINGLE_ENDED);
    // hadc1.State = 0;
    // hadc2.State = 0;
}

void ADC2_Init(void)
{
    /* Timer 8 configured to execute ADC2 conversion each 5ms */
    HAL_TIM_Base_Start(&htim8);
    /* Start ADC in DMA mode */
    // ADC2 - BSP inputs
    HAL_ADC_Start_DMA(&hadc2, (uint32_t*)adc2RawData, ADC2_CHANNEL_COUNT);

    // ADC Calibration for better accuracy TODO - not tested
    // HAL_ADCEx_Calibration_Start(&hadc1, ADC_SINGLE_ENDED);
    // HAL_ADCEx_Calibration_Start(&hadc2, ADC_SINGLE_ENDED);
    // HAL_ADCEx_Calibration_Start(&hadc3, ADC_SINGLE_ENDED);
    // hadc1.State = 0;
    // hadc2.State = 0;
}


/* USER CODE END 1 */
