PGRacing/PDM/CODE/PDMS/Core/Src/app/logic.c

#include "main.h"
#include "stm32l496xx.h"
#include "stm32l4xx_hal_def.h"
#include "stm32l4xx_hal_gpio.h"
#include "typedefs.h"
#include "logger.h"
#include "out.h"
#include "input.h"
#include "FreeRTOS.h"
#include "tim.h"
#include "cmsis_os2.h"
#include "logic.h"

// OPERATOR SHORTCUT
#define LOGIC_EXP_ALWAYS_ON { .opr = LOGIC_OPERATOR_E, .input1Type = LOGIC_INPUT_TYPE_CONST_SCHMITT, .input1Const = TRUE, .input2Type = LOGIC_INPUT_TYPE_CONST_SCHMITT, .input2Const = TRUE }

typedef struct
{
  T_LOGIC_VAR_TYPE allowedFirst;
  T_LOGIC_VAR_TYPE allowedSecond;
} T_LOGIC_OPERATOR_RELATION;

const static T_LOGIC_OPERATOR_RELATION operatorsConfig[] =
    {
        [LOGIC_OPERATOR_AND] =
            {
                .allowedFirst = LOGIC_VAR_TYPE_SCHMITT,
                .allowedSecond = LOGIC_VAR_TYPE_SCHMITT},
        [LOGIC_OPERATOR_OR] =
            {
                .allowedFirst = LOGIC_VAR_TYPE_SCHMITT,
                .allowedSecond = LOGIC_VAR_TYPE_SCHMITT},
        [LOGIC_OPERATOR_NE] =
            {
                .allowedFirst = LOGIC_VAR_TYPE_ANY,
                .allowedSecond = LOGIC_VAR_TYPE_ANY,
            },
        [LOGIC_OPERATOR_E] =
            {
                .allowedFirst = LOGIC_VAR_TYPE_ANY,
                .allowedSecond = LOGIC_VAR_TYPE_ANY,
            },
        [LOGIC_OPERATOR_G] =
            {
                .allowedFirst = LOGIC_VAR_TYPE_ANALOG,
                .allowedSecond = LOGIC_VAR_TYPE_ANALOG,
            },
        [LOGIC_OPERATOR_GE] =
            {
                .allowedFirst = LOGIC_VAR_TYPE_ANALOG,
                .allowedSecond = LOGIC_VAR_TYPE_ANALOG,
            },
        [LOGIC_OPERATOR_L] =
            {
                .allowedFirst = LOGIC_VAR_TYPE_ANALOG,
                .allowedSecond = LOGIC_VAR_TYPE_ANALOG,
            },
        [LOGIC_OPERATOR_LE] =
            {
                .allowedFirst = LOGIC_VAR_TYPE_ANALOG,
                .allowedSecond = LOGIC_VAR_TYPE_ANALOG,
            },
            
        [LOGIC_OPERATOR_IT] =
            {
                .allowedFirst = LOGIC_VAR_TYPE_SCHMITT,
                .allowedSecond = LOGIC_VAR_TYPE_NONE,
            },
            
        [LOGIC_OPERATOR_IF] =
            {
                .allowedFirst = LOGIC_VAR_TYPE_SCHMITT,
                .allowedSecond = LOGIC_VAR_TYPE_NONE,
            },
            
};

static T_LOGIC_VAR_TYPE LOGIC_GetInputModeAsLogicVarType( T_LOGIC_INPUT_TYPE  inType, T_INPUT_ID id)
{
  T_LOGIC_VAR_TYPE result = LOGIC_VAR_TYPE_NONE;

  switch (inType)
  {
  case LOGIC_INPUT_TYPE_SENSOR:
    {
      T_IN_MODE mode = IN_GetMode(id);
      if( mode == IN_MODE_ANALOG)
      {
        result = LOGIC_VAR_TYPE_ANALOG;
      }
      else if(mode == IN_MODE_SCHMITT)
      {
        result = LOGIC_VAR_TYPE_SCHMITT;
      } 
    }
    break;
    
  case LOGIC_INPUT_TYPE_CONST_SCHMITT:
    result = LOGIC_VAR_TYPE_SCHMITT;
    break;
  
  case LOGIC_INPUT_TYPE_CONST_ANALOG:
    result = LOGIC_VAR_TYPE_ANALOG;
    break;

  case LOGIC_INPUT_TYPE_UNSET:
    result = LOGIC_VAR_TYPE_NONE; 
    break;
   
  default:
    break;
  }

  return result;
}

static bool LOGIC_IsExpValid( T_LOGIC_EXPRESSION exp )
{
  ASSERT( exp.opr >= 0 );
  ASSERT( exp.opr < LOGIC_OPERATORM_MAX);

  bool res = FALSE;
  T_LOGIC_OPERATOR_RELATION relation = operatorsConfig[exp.opr];

  // Evaluate input types
  if(relation.allowedFirst != LOGIC_VAR_TYPE_ANY 
  && relation.allowedFirst == LOGIC_GetInputModeAsLogicVarType(exp.input1Type, exp.input1ID))
  {
    res = TRUE;
  }
  else if(relation.allowedFirst == LOGIC_VAR_TYPE_ANY)
  {
    res = TRUE;
  }
  else
  {
    res = FALSE;
  }
  
  if(relation.allowedSecond != LOGIC_VAR_TYPE_ANY 
  && relation.allowedSecond == LOGIC_GetInputModeAsLogicVarType(exp.input2Type, exp.input2ID))
  {
    res &= TRUE;
  }
  else if(relation.allowedSecond == LOGIC_VAR_TYPE_ANY)
  {
    res &= TRUE;
  }
  else
  {
    res = FALSE;
  }

  
  return res;
}

static bool LOGIC_EvaluateExpression (T_LOGIC_EXPRESSION exp)
{
  
  uint32_t r_data1 = 0;
  uint32_t r_data2 = 0;
  bool result = FALSE;

  // Acquire data for first part of expression
  if(exp.input1Type == LOGIC_INPUT_TYPE_SENSOR)
  {
    r_data1 = IN_GetValue(exp.input1ID);
  }
  else if(exp.input1Type == LOGIC_INPUT_TYPE_CONST_SCHMITT 
  || exp.input1Type == LOGIC_INPUT_TYPE_CONST_ANALOG)
  {
    r_data1 = exp.input1Const;
  }

  // Acquire data for second part of expression
  if(exp.input2Type == LOGIC_INPUT_TYPE_SENSOR)
  {
    r_data2 = IN_GetValue(exp.input2ID);
  }
  else if(exp.input2Type == LOGIC_INPUT_TYPE_CONST_SCHMITT 
  || exp.input2Type == LOGIC_INPUT_TYPE_CONST_ANALOG)
  {
    r_data2 = exp.input2Const;
  }
  
  // Evaluate expression
  switch (exp.opr)
  {
  case LOGIC_OPERATOR_AND:
  {
    // A && B
    result = ((bool)r_data1 && (bool)r_data2);
    break;
  }
    
  case LOGIC_OPERATOR_OR:
  {
    // A || B
    result = ((bool)r_data1 || (bool)r_data2);
    break;
  }
    
  case LOGIC_OPERATOR_NE:
  {
    // A != B
    result = ((uint32_t)r_data1 != (uint32_t)r_data2);
    break;
  }

  case LOGIC_OPERATOR_E:
  {
    // A == B
    result = ((uint32_t)r_data1 == (uint32_t)r_data2);
    break;
  }

  case LOGIC_OPERATOR_G:
  {
    // A > B
    result = ((uint32_t)r_data1 > (uint32_t)r_data2);
    break;
  }

  case LOGIC_OPERATOR_GE:
  {
    // A >= B
    result = ((uint32_t)r_data1 >= (uint32_t)r_data2);
    break;
  }

  case LOGIC_OPERATOR_L:
  {
    // A >= B
    result = ((uint32_t)r_data1 < (uint32_t)r_data2);
    break;
  }

  case LOGIC_OPERATOR_LE:
  {
    // A >= B
    result = ((uint32_t)r_data1 <= (uint32_t)r_data2);
    break;
  }

  case LOGIC_OPERATOR_IT:
  {
    // A == TRUE
    result = ((bool)r_data1 == TRUE);
    break;
  }

  case LOGIC_OPERATOR_IF:
  {
    // A == FALSE
    result = ((bool)r_data1 == FALSE);
    break;
  }

  default:
  {
    result = FALSE;
    break;
  }
    
  }
  return result;
}

// LOGIC Array struct
T_LOGIC_CFG logicCfg[POWER_OUT_COUNT] = 
{
  [0] = {
    .isUsed = FALSE,
  },
  [1] = {
    .isUsed = FALSE,
  },
  [2] = {
    .isUsed = TRUE,
    .exp = LOGIC_EXP_ALWAYS_ON
  },
  [3] = {
    .isUsed = TRUE,
    .exp = { .opr = LOGIC_OPERATOR_IT, 
    .input1Type = LOGIC_INPUT_TYPE_SENSOR, 
    .input1ID = 8, 
    .input2Type = LOGIC_INPUT_TYPE_UNSET, 
    }
  },
  [4] = {
    .isUsed = TRUE,
    .exp = LOGIC_EXP_ALWAYS_ON
  },
  [5] = {
    .isUsed = TRUE,
    .exp = 
    { .opr = LOGIC_OPERATOR_IT, 
    .input1Type = LOGIC_INPUT_TYPE_SENSOR, 
    .input1ID = 0, 
    .input2Type = LOGIC_INPUT_TYPE_UNSET, 
    }
  },
  [6] = {
    .isUsed = TRUE,
    .exp = LOGIC_EXP_ALWAYS_ON,
  },
  [7] = {
    .isUsed = TRUE,
    .exp = LOGIC_EXP_ALWAYS_ON
  },
  [8] = {
    .isUsed = TRUE,
    .exp = LOGIC_EXP_ALWAYS_ON
  },
  [9] = {
    // LOGGER
    .isUsed = TRUE,
    .exp = LOGIC_EXP_ALWAYS_ON
  },
  [10] = {
    .isUsed = TRUE,
    .exp = LOGIC_EXP_ALWAYS_ON
  },
  [11] = {
    // DASHBOARD
    .isUsed = TRUE,
    .exp = LOGIC_EXP_ALWAYS_ON
  },
  [12] = {
    .isUsed = FALSE,
  },
  [13] = {
    .isUsed = TRUE,
    .exp = LOGIC_EXP_ALWAYS_ON
  },
  [14] = {
    .isUsed = FALSE
  },
  [15] = {
    .isUsed = TRUE,
    .exp = LOGIC_EXP_ALWAYS_ON
  }
};

T_LOGIC_REG logicReg[POWER_OUT_COUNT] = {};

T_LOGIC_REG* LOGIC_Evaluate(void)
{
  for( uint8_t i = 0; i < POWER_OUT_COUNT; i++)
  {
    if( logicCfg[i].isUsed )
    {
      // Validate expression 
      if( LOGIC_IsExpValid( logicCfg[i].exp ) == FALSE )
      {
        logicReg[i].state = FALSE;
        logicReg[i].valid = FALSE;
        LOG_WARN("LOGIC: Logic expression invalid!");
        ASSERT( FALSE );
      }else
      {
        logicReg[i].state = LOGIC_EvaluateExpression(logicCfg[i].exp);
        logicReg[i].valid = TRUE;
      }
    }
    else
    {
      logicReg[i].state = FALSE;
      logicReg[i].valid = TRUE;
    }
  }
  
  return logicReg;
}

uint16_t LOGIC_GetValid(void)
{
  uint16_t resMask = 0x00;
  for(uint8_t i = 0; i < POWER_OUT_COUNT; i++)
  {
    if( logicReg[i].valid == TRUE)
    {
      resMask |= (1 << i);
    }
  }
  
  return resMask;
}

// void testTaskEntry(void *argument)
// {

//   T_LOGIC_EXPRESSION exp2 = 
//   {
//     .opr = LOGIC_OPERATOR_IT,
//     .input1Type = LOGIC_INPUT_TYPE_SENSOR,
//     .input1ID = IN_PHY_ID_1,
//     .input2Type =  LOGIC_INPUT_TYPE_UNSET,
//   };

//   OUT_ChangeMode( OUT_ID_1, OUT_MODE_STD);
//   OUT_ChangeMode( OUT_ID_2, OUT_MODE_PWM);
//   OUT_ChangeMode( OUT_ID_3, OUT_MODE_STD);
//   OUT_ChangeMode( OUT_ID_4, OUT_MODE_STD);
  
//   OUT_Batch(OUT_ID_5,OUT_ID_8);
//   OUT_ChangeMode( OUT_ID_6, OUT_MODE_STD);
//   OUT_ChangeMode( OUT_ID_7, OUT_MODE_STD);

//   for (;;)
//   {
//     //expResult = LOGIC_EvaluateExpression( exp2 );

//     OUT_ChangeMode( OUT_ID_2, OUT_MODE_PWM);
    
//     for( uint8_t i = 0; i < 100; i++)
//     {
//       BSP_OUT_SetDutyPWM(OUT_ID_2, i);
//       osDelay(100);
//     }

//     for( uint8_t i = 100; i > 0; i--)
//     {
//       BSP_OUT_SetDutyPWM(OUT_ID_2, i);
//       osDelay(100);
//     }

//     OUT_ChangeMode( OUT_ID_2, OUT_MODE_STD);

//     for( uint8_t i = 0; i < 10; i++)
//     {
//       OUT_ToggleState(OUT_ID_2);
//       osDelay(1000);
//     }
//   }
// }


///
/// TODO [MAJOR REWORK] Do some units tests on logic module
///
