PGRacing/PDM/CODE/PDMS/Core/Inc/adc.h

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
/* Define to prevent recursive inclusion -------------------------------------*/
#ifndef __ADC_H__
#define __ADC_H__

#ifdef __cplusplus
extern "C" {
#endif

/* Includes ------------------------------------------------------------------*/
#include "main.h"

extern ADC_HandleTypeDef hadc1;

extern ADC_HandleTypeDef hadc2;

extern ADC_HandleTypeDef hadc3;

/* USER CODE BEGIN Private defines */
#define ADC1_CHANNEL_COUNT 8
#define ADC2_CHANNEL_COUNT 8

#define ADC1_SAMPLING_RATE 10000 // Hz, frequency of ADC1 conversion
#define ADC1_SW_OVERSAMPLING_RATIO (ADC1_SAMPLING_RATE/200)
/* USER CODE END Private defines */

void MX_ADC1_Init(void);
void MX_ADC2_Init(void);
void MX_ADC3_Init(void);

/* USER CODE BEGIN Prototypes */
extern uint16_t adc1RawData[ADC1_CHANNEL_COUNT];
extern uint16_t adc2RawData[ADC2_CHANNEL_COUNT];

extern volatile uint16_t adc1MedianBufferShadow[ADC1_CHANNEL_COUNT][ADC1_SW_OVERSAMPLING_RATIO];

void ADC1_Init(void);
void ADC2_Init(void);

/* USER CODE END Prototypes */

#ifdef __cplusplus
}
#endif

#endif /* __ADC_H__ */
