PGRacing/PDM/CODE/PDMS/Core/Inc/bsp/bsp_spoc2.h

#ifndef __BSP_SPOC2_H_
#define __BSP_SPOC2_H_

#include "typedefs.h"
#include "spoc2.h"
#include "spoc2_definitions.h"

/// @brief SPI Transfer function used by SPOC2 device driver
/// @param id SPOC2 device id
/// @param txBuffer Transfer buffer
/// @param rxBuffer Receive buffer
/// @param dataLen Data length
/// @return Transfer status FALSE = FAIL, TRUE = OK
bool BSP_SPOC2_TransferBlocking(T_SPOC2_ID id, uint8_t* txBuffer, uint8_t* rxBuffer, uint32_t dataLen);

#endif
