PGRacing/PDM/CODE/PDMS/Core/Inc/driver/vmux.h

#ifndef __VMUX_H_
#define __VMUX_H_

#include "stm32l496xx.h"

// Initalize voltage multiplexer with ADC3
void VMUX_Init(void);

// Read voltage of one of 16 channels
uint32_t VMUX_GetValue(uint8_t index);

// Read battery voltage from ADC
void VMUX_ReadBattVoltage(void);

// Get battery voltage ADC channel 13
uint32_t VMUX_GetBattValue(void);

// Get battery voltage in mV using exponential moving average to smooth readings
uint32_t VMUX_GetBattValueEma(void);

int16_t VMUX_GetCoreTempValue(void);


extern volatile uint16_t VMUX_LP1Voltage[4];
extern volatile uint16_t VMUX_LP2Voltage[4];

#endif
