PGRacing/PDM/CODE/TEST/ARDUINO_UNO_BTS50025_SHIELD/Aiko_UART_ArduinoDUE/Aiko_UART_ArduinoDUE.ino

//#include <avr/wdt.h>
#include <DueTimer.h>

void BTS3XXXEJ_init(void);
void BTF3XXXEJ_init(void);
void BTT3018EJ_init(void);
void BTT3018EJ_Callin(void);
void BTS3XXXEJ_Callin(void);
void BTF3XXXEJ_Callin(void);
int translater(char a);
void PWM_Activation(void);
void update_PWM_parameters(void);

uint8_t VIS[]="VIS", Vin[]="VN", VinDEUX[]="VI", VO[]="VO", VS[]="VS";
uint8_t rec_data, send_data[20];
int cpt_cannal=0,temp1=123, temp2=56, temp3=56, Vref1=0,Vref2=0,Vref3=0, Vref4=0, TICK=1;
uint32_t result, event_count_PWM_IC1=0, event_count_PWM_IC2=0, event_count_PWM_IC3=0, event_count_PWM_IC4=0, event_count_PWM=0, nb_pulse=0, nb_pulse_IC1=0, nb_pulse_IC2=0, nb_pulse_IC3=0, nb_pulse_IC4=0, nb_pulse_temp=0, nb_pulse_temp_IC1=0,nb_pulse_temp_IC2=0,nb_pulse_temp_IC3=0,nb_pulse_temp_IC4=0, frequency=0, dutycycle=0, ton=0, toff=0, ton_IC2=0, toff_IC2=0, ton_IC3=0, toff_IC3=0, ton_IC4=0, toff_IC4=0, ton_IC1=0, toff_IC1=0, f_IC2=0, dc_IC2=0,f_IC3=0, dc_IC3=0, f_IC4=0, dc_IC4=0, f_IC1=0, dc_IC1=0, delay_IC1=0, delay_IC2=0, delay_IC3=0, delay_IC4=0, delay_IC1_temp=0, delay_IC2_temp=0, delay_IC3_temp=0, delay_IC4_temp=0;
bool TOATE_IC1=false, TOATE_IC2=false, TOATE_IC3=false, TOATE_IC4=false,Pulse_ON=false, Pulse_IC1=false,Pulse_IC2=false, Pulse_IC3=false, PWM_IC4=false, PWM_IC1=false,PWM_IC2=false, PWM_IC3=false, Pulse_IC4=false,BTS50015_1TAD=false,BTS3011TE=false, ShieldFourDevices=false, Part_ON=false, fully_ON=false, PWM_ON=false, BTT3018EJ=false, BTS3XXXEJ=false, BTF3XXXEJ=false;
float ratio_timer = 1.578;

 
void setup() 
{
    //Timer3.attachInterrupt(PWM_Activation); Timer3.stop();
    Serial.begin(115600); Serial.setTimeout(1000);
}

void loop()
{
      // put your main code here, to run repeatedly
      char rec_data;      

      PWM_Activation();

      delayMicroseconds(1);
      if (Serial.available()>0)
      {  
          Serial.readBytes(&rec_data, 1);
          //////Data Processing
          if(ShieldFourDevices==false)
          {                         
                switch (rec_data)
                {                   
                    case 'N':
                    {              
                         if(BTT3018EJ==true || BTS3011TE==true){digitalWrite(11,1);} else if(BTS3XXXEJ==true || BTF3XXXEJ==true){digitalWrite(10,1);} else if(BTS50015_1TAD==true){digitalWrite(6,1);}  
                         Part_ON=true;
                         break; 
                    }
                    case 'F':
                    {              
                         if(BTT3018EJ==true|| BTS3011TE==true){digitalWrite(11,0);} else if(BTS3XXXEJ==true || BTF3XXXEJ==true){digitalWrite(10,0);} else if(BTS50015_1TAD==true){digitalWrite(6,0);}  
                         Part_ON=false;
                         break; 
                    }
                    case 'P': //Pulse ON
                    {
                        Pulse_ON=true;Part_ON=true;nb_pulse_temp=nb_pulse; update_PWM_parameters();
                        //Timer3.start(TICK);
                        break;
                    }
                    case 'Z': {fully_ON=true;break;}
                    case 'H': //Pulses number modif
                    {
                         uint8_t mil='H',cent='H', dix='H', unit='H';

                         Serial.flush(); while(Serial.available()==0){ }  Serial.readBytes(&mil, 1);
                         Serial.flush(); while(Serial.available()==0){ }  Serial.readBytes(&cent, 1);
                         Serial.flush(); while(Serial.available()==0){ }  Serial.readBytes(&dix, 1);
                         Serial.flush(); while(Serial.available()==0){ }  Serial.readBytes(&unit, 1);
                         nb_pulse=1000*translater(mil)+100*translater(cent)+10*translater(dix)+translater(unit);
                         break;
                    }
                    case 'S': //PWM ON
                    {
                          Pulse_ON=false; Part_ON=true;PWM_ON=true; update_PWM_parameters();
                          //Timer3.start(TICK);
                          break;
                    }
                    case 'L': //PWM function OFF to write for ONE channel
                    {
                          Part_ON=false;PWM_ON=false;Pulse_ON=false; 
                          break;
                    }                 
                    case 'a':
                    {
                        uint8_t cent='a', dix='a', unit='a';
                        Serial.flush(); while(Serial.available()==0){ }  Serial.readBytes(&cent, 1);
                        Serial.flush(); while(Serial.available()==0){ }  Serial.readBytes(&dix, 1);
                        Serial.flush(); while(Serial.available()==0){ }  Serial.readBytes(&unit, 1);
                        dutycycle=100*translater(cent)+10*translater(dix)+translater(unit);
                        update_PWM_parameters();
                        break;
                    }
                    case 'k':
                    {
                        uint8_t dixmil='k', mil='k',cent='k', dix='k', unit='k';
                        Serial.flush(); while(Serial.available()==0){ }  Serial.readBytes(&mil, 1);
                        Serial.flush(); while(Serial.available()==0){ }  Serial.readBytes(&mil, 1);
                        Serial.flush(); while(Serial.available()==0){ }  Serial.readBytes(&cent, 1);
                        Serial.flush(); while(Serial.available()==0){ }  Serial.readBytes(&dix, 1);
                        Serial.flush(); while(Serial.available()==0){ }  Serial.readBytes(&unit, 1);
                        frequency=10000*translater(dixmil)+1000*translater(mil)+100*translater(cent)+10*translater(dix)+translater(unit);
                        update_PWM_parameters();
                        break;
                    }
                    ///Interface Callin
                    case '@':
                    {       
                            if(BTT3018EJ==false && BTS3XXXEJ==false && BTF3XXXEJ==false && BTS50015_1TAD==false && BTS3011TE==false){Serial.write("product");}
                            else if(BTT3018EJ==true || BTS3011TE==true){BTT3018EJ_Callin();}
                            else if(BTS3XXXEJ==true){BTS3XXXEJ_Callin();}
                            else if(BTF3XXXEJ==true) {BTF3XXXEJ_Callin();}
                            else if(BTS50015_1TAD==true){BTS50015_1TAD_Callin();}
                            break; 
                    } 
                    //case 'R':{ wdt_enable(WDTO_15MS);break; } //Reset
                    //Alternative function
                    case '<':{ pinMode(9,OUTPUT); digitalWrite(9,1);delay(500);digitalWrite(9,0); pinMode(9,INPUT);break; } //Wabco Vin and Status are disconnected
                    case '>':{ pinMode(9,OUTPUT);digitalWrite(9,1);delay(5);digitalWrite(9,0);pinMode(9,INPUT);break; } //Wabco Vin and Status are connected
                    case '/':{ pinMode(9,OUTPUT);digitalWrite(9,1);delay(10);digitalWrite(9,0);pinMode(9,INPUT);break; } //BTF3XXXEJ Reset Status
                    case '!':
                    { 
                        if(Part_ON==true){ digitalWrite(10,0);}
                        else if(PWM_ON==true){ }
                        
                        delay(5);pinMode(9,OUTPUT);digitalWrite(9,1);delay(10);digitalWrite(9,0);pinMode(9,INPUT);
                        
                        if(Part_ON==true){ digitalWrite(10,1);}
                        else if(PWM_ON==true){ } //Timer.Start
                        
                        break; 
                    }//BTF3XXXEJ Reset Trig
                    case ')':{ pinMode(11,OUTPUT);digitalWrite(11,1);break; } //BTF3XXXEJ Enable ON
                    case '%':{ pinMode(11,OUTPUT);digitalWrite(11,0);break; } //BTF3XXXEJ Enable OFF
                    ///Product selection
                    case '&':{ BTT3018EJ=true;BTT3018EJ_init();Serial.write("BTT3018EJ");break; } //Wabco Vin and Status are connected
                    case '?':{ BTS3011TE=true;BTT3018EJ_init();Serial.write("BTS3011TE");break; } //Wabco Vin and Status are connected
                    case '-':{ BTS3XXXEJ=true;BTS3XXXEJ_init();Serial.write("BTS3XXXEJ");break; } //Wabco Vin and Status are connected
                    case '_':{ BTF3XXXEJ=true;BTF3XXXEJ_init();Serial.write("BTF3XXXEJ");break; } //Wabco Vin and Status are connected
                    case '[':{ BTS50015_1TAD=true;BTS50015_1TAD_init();Serial.write("BTS50015_1TAD");break; } //Wabco Vin and Status are connected
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
